Left-Hand/74-gate-computer/kicad/ALU0/ALU0.png

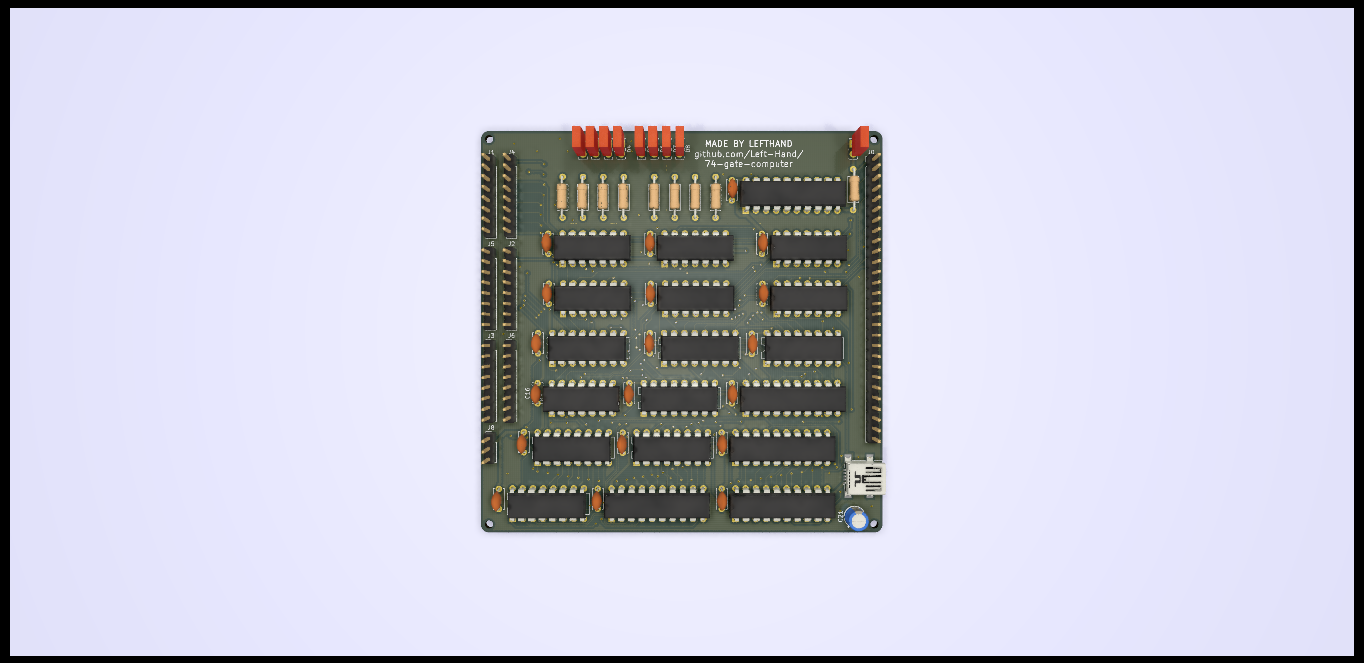
kicad/ALU0/ALU0.png
